jurassic73/split89/3d_printing_stl_files/split89_left_wrist_pad.stl

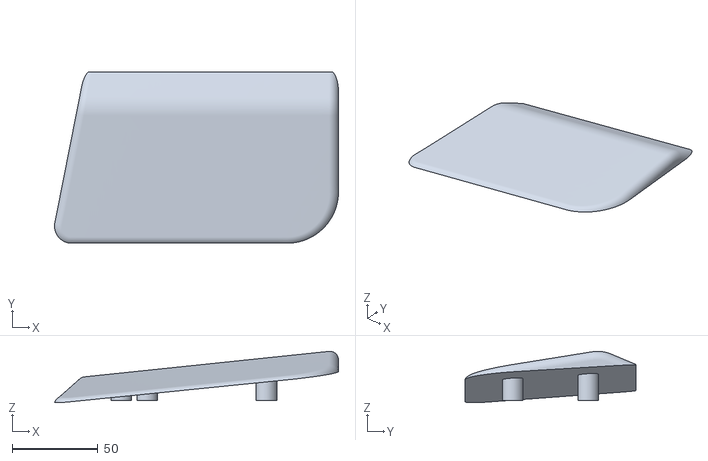
[picture p50: CAD file, 2021-06-19]
3d_printing_stl_files/split89_left_wrist_pad.stl
165.6 x 100.0 x 30.0
