jurassic73/split89/3d_printing_stl_files/split89_left_body_base.stl

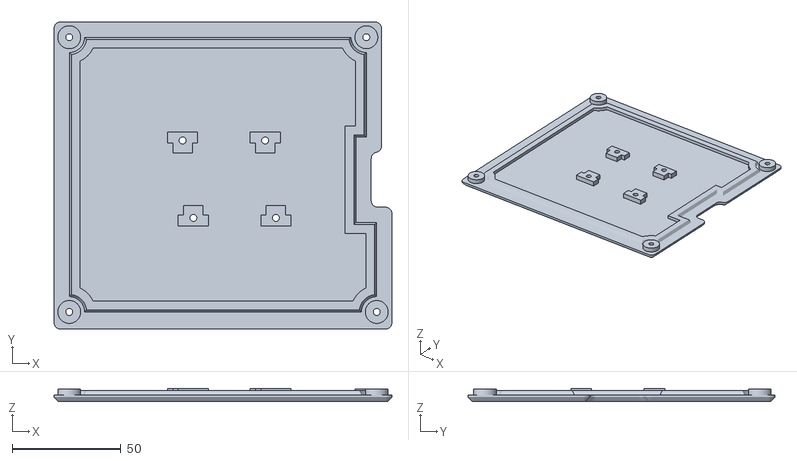
[picture p51: CAD file, 2021-06-19]
3d_printing_stl_files/split89_left_body_base.stl
155.1 x 140.8 x 6.00
