jurassic73/split89/3d_printing_stl_files/split89_trrs_jack_brace.stl

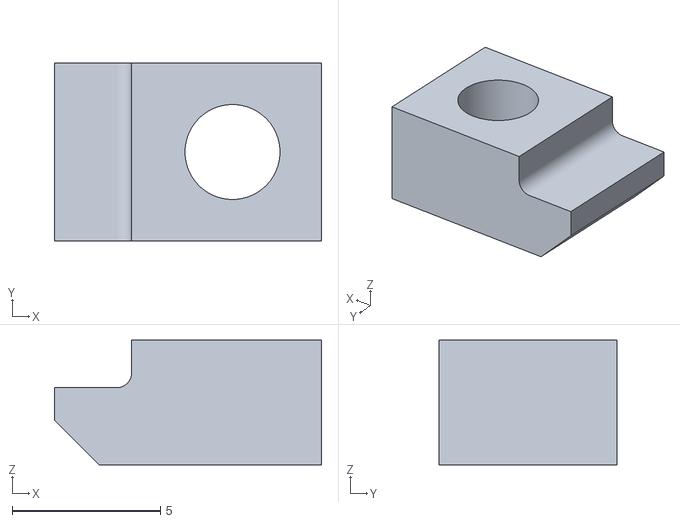
[picture p52: CAD file, 2021-06-19]
3d_printing_stl_files/split89_trrs_jack_brace.stl
9.00 x 6.00 x 4.20
